Miceuz/paper-wifi/pics/20221112_141635.jpg

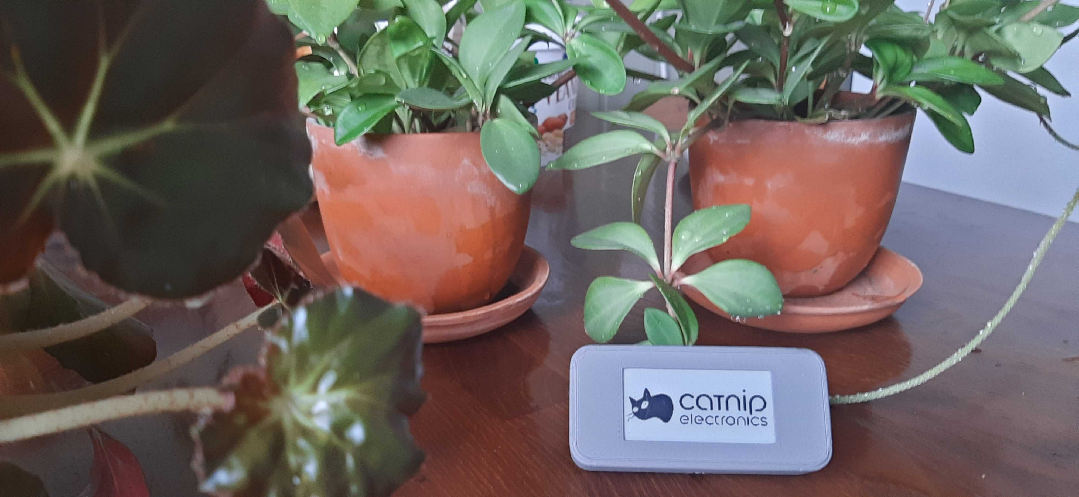
pics/20221112_141635.jpg
