Miceuz/paper-wifi/pics/20221114_130836.jpg

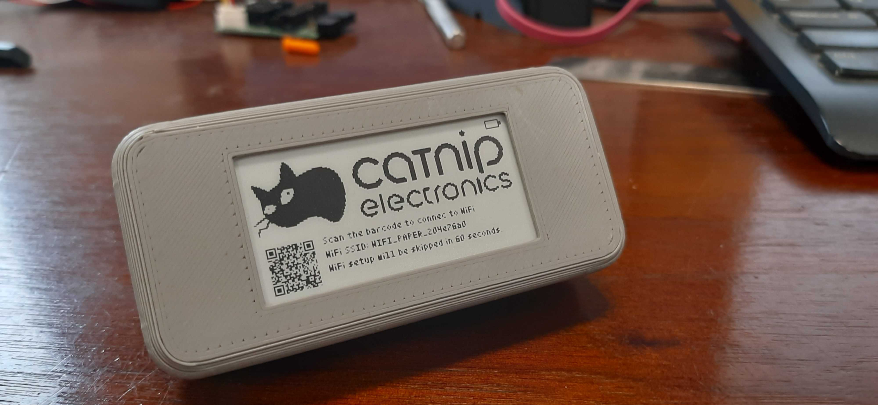
pics/20221114_130836.jpg
