Miceuz/paper-wifi/pics/20221114_130928.jpg

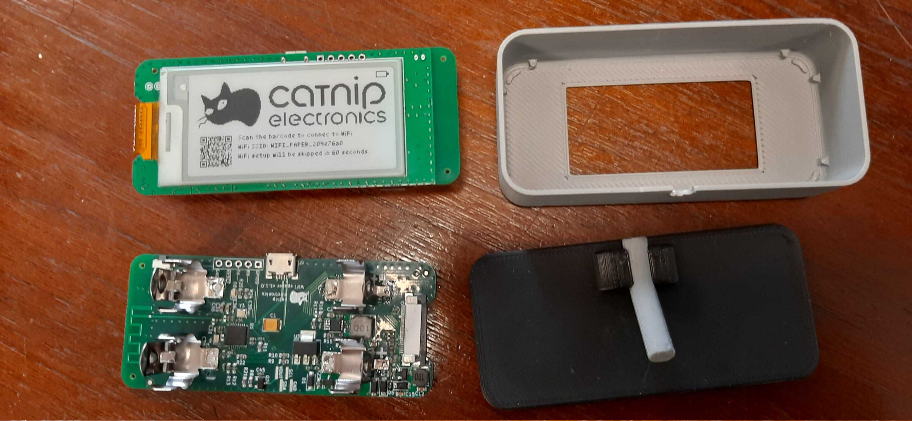
pics/20221114_130928.jpg
