Miceuz/paper-wifi/Firmware/ble_peripheral/src/catnip.c

#include "pgmspace.h"
// 'catnip', 200x53px
const unsigned char epd_bitmap_catnip[] PROGMEM = {
    0x00, 0x00, 0x00, 0x00, 0x00, 0x00, 0x00, 0x00, 0x00, 0x00, 0x00, 0x00,
    0x00, 0x00, 0x00, 0x00, 0x00, 0x00, 0x00, 0x00, 0x00, 0x40, 0x00, 0x00,
    0x00, 0x00, 0x00, 0x00, 0x0c, 0x00, 0x00, 0x00, 0x00, 0x00, 0x00, 0x00,
    0x00, 0x00, 0x00, 0x00, 0x00, 0x00, 0x00, 0x00, 0x00, 0x01, 0xe0, 0x00,
    0x00, 0x00, 0x00, 0x00, 0x00, 0x0e, 0x00, 0x00, 0x00, 0x00, 0x00, 0x00,
    0x00, 0x00, 0x00, 0x00, 0x00, 0x00, 0x00, 0x00, 0x00, 0x00, 0x01, 0xf0,
    0x00, 0x00, 0x00, 0x00, 0x00, 0x00, 0x1f, 0x00, 0x00, 0x00, 0x00, 0x00,
    0x00, 0x00, 0x00, 0x00, 0x00, 0x00, 0x00, 0x00, 0x00, 0x00, 0x00, 0x01,
    0xe0, 0x00, 0x00, 0x00, 0x00, 0x00, 0x00, 0x1f, 0x80, 0x00, 0x00, 0x00,
    0x00, 0x00, 0x00, 0x00, 0x00, 0x00, 0x00, 0x00, 0x00, 0x00, 0x00, 0x00,
    0x00, 0xe0, 0x00, 0x00, 0x00, 0x00, 0x00, 0x00, 0x3f, 0x80, 0x00, 0x00,
    0x00, 0x00, 0x00, 0x00, 0x00, 0x00, 0x00, 0x00, 0x00, 0x00, 0x00, 0x00,
    0x00, 0x00, 0x00, 0x00, 0x00, 0x00, 0x00, 0x00, 0x00, 0x3f, 0xc0, 0x00,
    0x00, 0x00, 0x00, 0x00, 0x00, 0x00, 0x00, 0x00, 0x00, 0x00, 0x00, 0x00,
    0x00, 0x00, 0x00, 0x00, 0x00, 0x00, 0x00, 0x00, 0x00, 0x00, 0x3f, 0xc0,
    0x00, 0x00, 0x00, 0x00, 0x00, 0x00, 0x00, 0x00, 0x00, 0x00, 0x00, 0x00,
    0x00, 0x00, 0x00, 0x00, 0x00, 0x00, 0x00, 0x00, 0x00, 0x00, 0x00, 0x3f,
    0xe0, 0x00, 0x00, 0x00, 0x00, 0x00, 0x07, 0xf0, 0x00, 0x07, 0xe0, 0x00,
    0x00, 0x00, 0x03, 0xf0, 0x00, 0x40, 0x00, 0xfe, 0x00, 0x00, 0x00, 0x00,
    0x7f, 0xe0, 0x00, 0xff, 0x00, 0x00, 0x00, 0x1f, 0xfc, 0x00, 0x3f, 0xfc,
    0x07, 0xff, 0xf8, 0x1f, 0xfc, 0x01, 0xe0, 0x03, 0xff, 0x80, 0x00, 0x00,
    0x00, 0x7f, 0xe0, 0x0f, 0xff, 0xe0, 0x00, 0x00, 0x7f, 0xff, 0x00, 0x7f,
    0xfe, 0x07, 0xff, 0xf8, 0x3f, 0xfe, 0x01, 0xe0, 0x0f, 0xff, 0xe0, 0x00,
    0x00, 0x00, 0x7f, 0xf0, 0x7f, 0xff, 0xf8, 0x00, 0x00, 0xff, 0xff, 0x81,
    0xff, 0xff, 0x07, 0xff, 0xf8, 0x7f, 0xff, 0x81, 0xe0, 0x1f, 0xff, 0xf0,
    0x00, 0x00, 0x00, 0x7f, 0xf3, 0xff, 0xff, 0xfc, 0x00, 0x01, 0xfc, 0x1f,
    0xc3, 0xf8, 0x3f, 0x83, 0xff, 0xf0, 0xfc, 0x1f, 0x81, 0xe0, 0x3f, 0x83,
    0xf8, 0x00, 0x00, 0x00, 0xff, 0xff, 0xff, 0xff, 0xff, 0x00, 0x03, 0xf0,
    0x07, 0xc3, 0xe0, 0x0f, 0xc0, 0x1e, 0x01, 0xf8, 0x07, 0xc1, 0xe0, 0x7e,
    0x00, 0xfc, 0x0c, 0x00, 0x00, 0xff, 0xff, 0xff, 0xff, 0xff, 0x00, 0x03,
    0xe0, 0x03, 0x87, 0xc0, 0x03, 0xe0, 0x1e, 0x01, 0xf0, 0x03, 0xc1, 0xe0,
    0x7c, 0x00, 0x7c, 0x0f, 0x00, 0x01, 0xff, 0xff, 0xff, 0xff, 0xff, 0x80,
    0x07, 0xc0, 0x00, 0x07, 0x80, 0x03, 0xe0, 0x1e, 0x01, 0xe0, 0x03, 0xe1,
    0xe0, 0xf8, 0x00, 0x3e, 0x0f, 0xc0, 0x03, 0xff, 0xff, 0xff, 0xff, 0xff,
    0xc0, 0x07, 0x80, 0x00, 0x0f, 0x80, 0x01, 0xe0, 0x1e, 0x03, 0xc0, 0x01,
    0xe1, 0xe0, 0xf0, 0x00, 0x1e, 0x07, 0xe0, 0x0f, 0xff, 0xff, 0xff, 0xff,
    0xff, 0xc0, 0x07, 0x80, 0x00, 0x0f, 0x00, 0x00, 0xf0, 0x1e, 0x03, 0xc0,
    0x01, 0xe1, 0xe0, 0xf0, 0x00, 0x1e, 0x07, 0xf8, 0x3f, 0xff, 0xff, 0xff,
    0xff, 0xff, 0xc0, 0x0f, 0x80, 0x00, 0x0f, 0x00, 0x00, 0xf0, 0x1e, 0x03,
    0xc0, 0x01, 0xe1, 0xe1, 0xf0, 0x00, 0x1f, 0x07, 0xfc, 0xff, 0xff, 0xff,
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

// Array of all bitmaps for convenience. (Total bytes used to store images in
// PROGMEM = 1344)
const int epd_bitmap_allArray_LEN = 1;
const unsigned char *epd_bitmap_allArray[1] = {epd_bitmap_catnip};
