Miceuz/paper-wifi/Firmware/example_humidity_sensor/src/FreeMonoBold36.h

const uint8_t FreeMono_Bold36pt7bBitmaps[] PROGMEM = {
  0x00, 0x3F, 0x0F, 0xFB, 0xFF, 0x7F, 0xFF, 0xFF, 0xFF, 0xFF, 0xFF, 0xFF,
  0xFF, 0xFF, 0xFF, 0xFF, 0xFF, 0xFF, 0xFD, 0xFF, 0xBF, 0xF3, 0xFE, 0x7F,
  0xCF, 0xF9, 0xFF, 0x3F, 0xE7, 0xFC, 0xFF, 0x9F, 0xE3, 0xFC, 0x7F, 0x87,
  0xF0, 0xFE, 0x1F, 0xC3, 0xF8, 0x7F, 0x0F, 0xC0, 0xF8, 0x00, 0x00, 0x00,
  0x00, 0x00, 0x00, 0x00, 0x7F, 0x1F, 0xF7, 0xFE, 0xFF, 0xFF, 0xFF, 0xFF,
  0xFF, 0xE7, 0xF8, 0x7E, 0x00, 0xFF, 0x83, 0xFF, 0xFF, 0x07, 0xFF, 0xFC,
  0x0F, 0xFF, 0xF8, 0x1F, 0xFF, 0xF0, 0x3F, 0xDF, 0xE0, 0x3F, 0xBF, 0xC0,
  0x7F, 0x3F, 0x80, 0xFE, 0x7F, 0x01, 0xFC, 0xFE, 0x03, 0xF9, 0xFC, 0x07,
  0xF3, 0xF0, 0x0F, 0xE7, 0xE0, 0x1F, 0x8F, 0xC0, 0x1F, 0x0F, 0x80, 0x3E,
  0x1F, 0x00, 0x7C, 0x3E, 0x00, 0xF8, 0x7C, 0x01, 0xF0, 0xF8, 0x03, 0xE1,
  0xE0, 0x03, 0x81, 0xC0, 0x07, 0x00, 0x00, 0x1E, 0x01, 0xE0, 0x00, 0x0F,
  0xC0, 0xFC, 0x00, 0x03, 0xF0, 0x3F, 0x80, 0x01, 0xFC, 0x0F, 0xE0, 0x00,
  0x7F, 0x07, 0xF8, 0x00, 0x1F, 0xC1, 0xFE, 0x00, 0x07, 0xF0, 0x7F, 0x00,
  0x01, 0xFC, 0x1F, 0xC0, 0x00, 0x7F, 0x07, 0xF0, 0x00, 0x1F, 0xC1, 0xFC,
  0x00, 0x07, 0xF0, 0x7F, 0x00, 0x01, 0xFC, 0x1F, 0xC0, 0x00, 0x7F, 0x07,
  0xF0, 0x00, 0x1F, 0xC1, 0xFC, 0x00, 0x07, 0xF0, 0x7F, 0x00, 0x03, 0xFC,
  0x1F, 0xC0, 0x03, 0xFF, 0xFF, 0xFC, 0x07, 0xFF, 0xFF, 0xFF, 0xE3, 0xFF,
  0xFF, 0xFF, 0xFC, 0xFF, 0xFF, 0xFF, 0xFF, 0x3F, 0xFF, 0xFF, 0xFF, 0xCF,
  0xFF, 0xFF, 0xFF, 0xF1, 0xFF, 0xFF, 0xFF, 0xF8, 0x0F, 0xFF, 0xFF, 0xF0,
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
  {  5462,  38,  41,  43,    1,  -40 },   // 0x46 'F'
  {  5657,  40,  43,  43,    2,  -41 },   // 0x47 'G'
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

const GFXfont FreeMono_Bold36pt7b PROGMEM = {
  (uint8_t  *)FreeMono_Bold36pt7bBitmaps,
  (GFXglyph *)FreeMono_Bold36pt7bGlyphs,
  0x20, 0x7E, 77 };

// Approx. 16322 bytes
