Miceuz/paper-wifi/Firmware/example_humidity_sensor/src/FreeMonoBold48.h

const uint8_t FreeMono_Bold48pt7bBitmaps[] PROGMEM = {
  0x00, 0x0F, 0xC0, 0x3F, 0xE1, 0xFF, 0xE3, 0xFF, 0xEF, 0xFF, 0xDF, 0xFF,
  0xFF, 0xFF, 0xFF, 0xFF, 0xFF, 0xFF, 0xFF, 0xFF, 0xFF, 0xFF, 0xFF, 0xFF,
  0xFF, 0xDF, 0xFF, 0xBF, 0xFF, 0x7F, 0xFE, 0xFF, 0xFC, 0xFF, 0xF9, 0xFF,
  0xF3, 0xFF, 0xE7, 0xFF, 0xCF, 0xFF, 0x9F, 0xFE, 0x3F, 0xFC, 0x7F, 0xF8,
  0xFF, 0xF1, 0xFF, 0xE1, 0xFF, 0xC3, 0xFF, 0x87, 0xFF, 0x0F, 0xFE, 0x1F,
  0xFC, 0x3F, 0xF8, 0x7F, 0xE0, 0xFF, 0xC1, 0xFF, 0x83, 0xFF, 0x07, 0xFE,
  0x07, 0xFC, 0x0F, 0xF8, 0x1F, 0xE0, 0x1F, 0xC0, 0x1F, 0x00, 0x00, 0x00,
  0x00, 0x00, 0x00, 0x00, 0x00, 0x00, 0x00, 0x00, 0x00, 0x1F, 0xC0, 0xFF,
  0xC3, 0xFF, 0xC7, 0xFF, 0xDF, 0xFF, 0xBF, 0xFF, 0x7F, 0xFE, 0xFF, 0xFC,
  0xFF, 0xF9, 0xFF, 0xE1, 0xFF, 0xC1, 0xFE, 0x00, 0xFF, 0xF0, 0x1F, 0xFF,
  0xFF, 0xE0, 0x3F, 0xFB, 0xFF, 0xC0, 0x7F, 0xF7, 0xFF, 0x00, 0xFF, 0xEF,
  0xFE, 0x01, 0xFF, 0xDF, 0xFC, 0x03, 0xFF, 0x9F, 0xF8, 0x07, 0xFF, 0x3F,
  0xF0, 0x07, 0xFE, 0x7F, 0xE0, 0x0F, 0xFC, 0xFF, 0xC0, 0x1F, 0xF9, 0xFF,
  0x80, 0x3F, 0xE3, 0xFE, 0x00, 0x7F, 0xC7, 0xFC, 0x00, 0xFF, 0x87, 0xF8,
  0x01, 0xFF, 0x0F, 0xF0, 0x03, 0xFE, 0x1F, 0xE0, 0x03, 0xFC, 0x3F, 0xC0,
  0x07, 0xF8, 0x7F, 0x80, 0x0F, 0xF0, 0xFF, 0x00, 0x1F, 0xC1, 0xFC, 0x00,
  0x3F, 0x83, 0xF8, 0x00, 0x7F, 0x03, 0xF0, 0x00, 0xFE, 0x07, 0xE0, 0x00,
  0xFC, 0x0F, 0xC0, 0x01, 0xF8, 0x1F, 0x80, 0x03, 0xF0, 0x3F, 0x00, 0x07,
  0xC0, 0x3C, 0x00, 0x0F, 0x80, 0x30, 0x00, 0x06, 0x00, 0x00, 0x07, 0xE0,
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
  {  9553,  51,  55,  56,    1,  -54 },   // 0x46 'F'
  {  9904,  53,  57,  56,    3,  -55 },   // 0x47 'G'
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

const GFXfont FreeMono_Bold48pt7b PROGMEM = {
  (uint8_t  *)FreeMono_Bold48pt7bBitmaps,
  (GFXglyph *)FreeMono_Bold48pt7bGlyphs,
  0x20, 0x7E, 102 };

// Approx. 28180 bytes
