Miceuz/paper-wifi/Firmware/example_soil_moisture_sensor/src/settings.h

#ifndef __SETTINGS_H
#define __SETTINGS_H

struct Settings {
  enum class TempFormat : char { CELSIUS = 'C', FARENHEIT = 'F' };
  enum class MoistFormat : char { RAW = 'r', PERCENT = '%' };
  enum class PrimaryReading : char { MOISTURE = 'M', TEMPERATURE = 'T' };
  TempFormat temp_format;
  MoistFormat moist_format;
  PrimaryReading primary_reading;
  char mqtt_address[50];
  char mqtt_device_id[20];
  char mqtt_username[20];
  char mqtt_password[20];
  char mqtt_topic[20];
  uint16_t mqtt_port;
  void setDefault() {
    moist_format = MoistFormat::RAW;
    temp_format = TempFormat::CELSIUS;
    primary_reading = PrimaryReading::MOISTURE;
  }
};

extern Settings settings;

#endif
