Miceuz/paper-wifi/Firmware/example_humidity_sensor/src/symbols.h

const uint8_t symbols_Bitmaps[] PROGMEM = {
    0xFF, 0xF2, 0x00, 0x4B, 0x6D, 0xED, 0xB7, 0xB6, 0xDE, 0x00, 0x4F, 0xFF,
    0x00, 0xFF, 0xF2, 0x00, 0x4B, 0x61, 0xED, 0x87, 0xB6, 0x1E, 0x00, 0x4F,
    0xFF, 0x00, 0xFF, 0xF2, 0x00, 0x4B, 0x01, 0xEC, 0x07, 0xB0, 0x1E, 0x00,
    0x4F, 0xFF, 0x00, 0xFF, 0xF2, 0x00, 0x48, 0x01, 0xE0, 0x07, 0x80, 0x1E,
    0x00, 0x4F, 0xFF, 0x00, 0x00, 0x00, 0x00, 0x00, 0xC0, 0x00, 0x00, 0x00,
    0x00, 0x60, 0x03, 0xFF, 0xFF, 0xFF, 0xB7, 0xF0, 0x80, 0x00, 0x00, 0x18,
    0x04, 0x20, 0x00, 0x00, 0x0C, 0x01, 0x08, 0x00, 0x00, 0x06, 0x00, 0x42,
    0x00, 0x00, 0x03, 0x00, 0x1C, 0x80, 0x00, 0x01, 0x80, 0x07, 0x20, 0x00,
    0x00, 0xC0, 0x01, 0xC8, 0x00, 0x00, 0x60, 0x00, 0x72, 0x00, 0x00, 0x30,
    0x00, 0x1C, 0x80, 0x00, 0x18, 0x00, 0x07, 0x20, 0x00, 0x0C, 0x00, 0x01,
    0xC8, 0x00, 0x06, 0x00, 0x00, 0x72, 0x00, 0x03, 0x00, 0x00, 0x1C, 0x80,
    0x01, 0x80, 0x00, 0x04, 0x20, 0x00, 0xC0, 0x00, 0x01, 0x08, 0x00, 0x60,
    0x00, 0x00, 0x43, 0xFF, 0xB7, 0xFF, 0xFF, 0xF0, 0x00, 0x18, 0x00, 0x00,
    0x00, 0x00, 0x0C, 0x00, 0x00, 0x00, 0x00, 0x3F, 0x88, 0x0A, 0x7C, 0x90,
    0x44, 0xE4, 0x22, 0x01, 0x00, 0x70, 0x04, 0x00};

const GFXglyph symbols_Glyphs[] PROGMEM = {
    {0, 14, 7, 14, 0, -8},    // 0x41 'A'
    {13, 14, 7, 14, 0, -8},   // 0x42 'B'
    {26, 14, 7, 14, 0, -8},   // 0x43 'C'
    {39, 14, 7, 14, 0, -8},   // 0x44 'D'
    {52, 42, 21, 42, 0, -10}, // 0x45 'E'
    {0, 0, 0, 0, 0, 0},       // 0x46 'F'
    {0, 0, 0, 0, 0, 0},       // 0x47 'G'
    {0, 0, 0, 0, 0, 0},       // 0x48 'H'
    {0, 0, 0, 0, 0, 0},       // 0x49 'I'
    {0, 0, 0, 0, 0, 0},       // 0x4A 'J'
    {0, 0, 0, 0, 0, 0},       // 0x4B 'K'
    {0, 0, 0, 0, 0, 0},       // 0x4C 'L'
    {0, 0, 0, 0, 0, 0},       // 0x4D 'M'
    {0, 0, 0, 0, 0, 0},       // 0x4E 'N'
    {0, 0, 0, 0, 0, 0},       // 0x4F 'O'
    {0, 0, 0, 0, 0, 0},       // 0x50 'P'
    {0, 0, 0, 0, 0, 0},       // 0x51 'Q'
    {0, 0, 0, 0, 0, 0},       // 0x52 'R'
    {0, 0, 0, 0, 0, 0},       // 0x53 'S'
    {0, 0, 0, 0, 0, 0},       // 0x54 'T'
    {0, 0, 0, 0, 0, 0},       // 0x55 'U'
    {0, 0, 0, 0, 0, 0},       // 0x56 'V'
    {163, 11, 9, 14, 0, -9}   // 0x57 'W'
};

const GFXfont symbols PROGMEM = {(uint8_t *)symbols_Bitmaps,
                                 (GFXglyph *)symbols_Glyphs, 0x41, 0x57, 10};
